eMadman/SmartSpin2k/Hardware/MODS/Direct Mount Mod/Bike Mount/reference photos/LeMond Revmaster/257341490_309686497794501_8044706802333533932_n.jpg

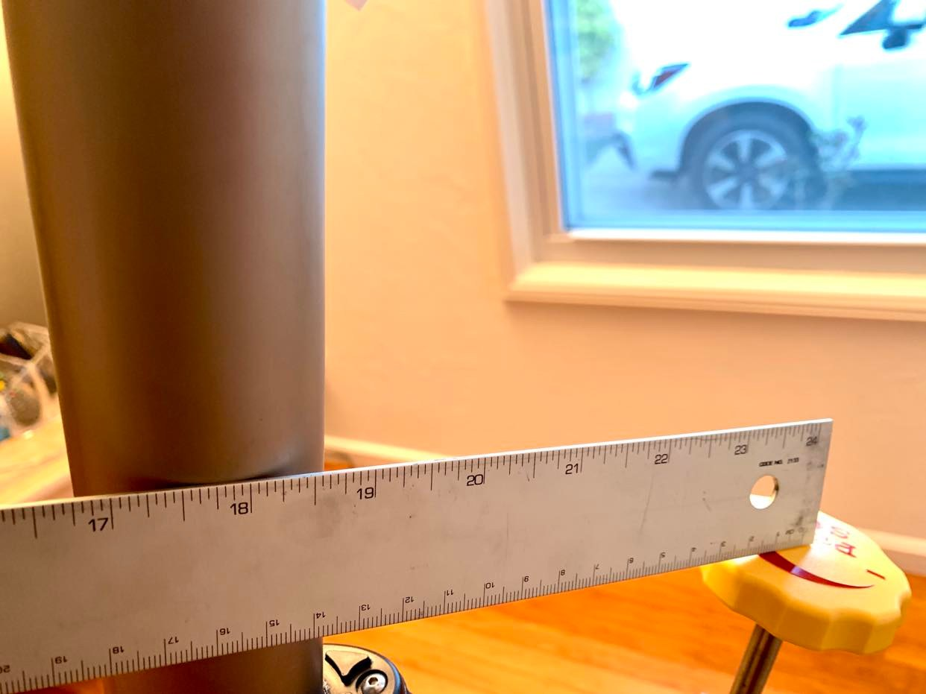
Hardware/MODS/Direct Mount Mod/Bike Mount/reference photos/LeMond Revmaster/257341490_309686497794501_8044706802333533932_n.jpg
