eMadman/SmartSpin2k/Hardware/MODS/Direct Mount Mod/Bike Mount/reference photos/LeMond Revmaster/257692339_471179641047132_6647679529000994123_n.jpg

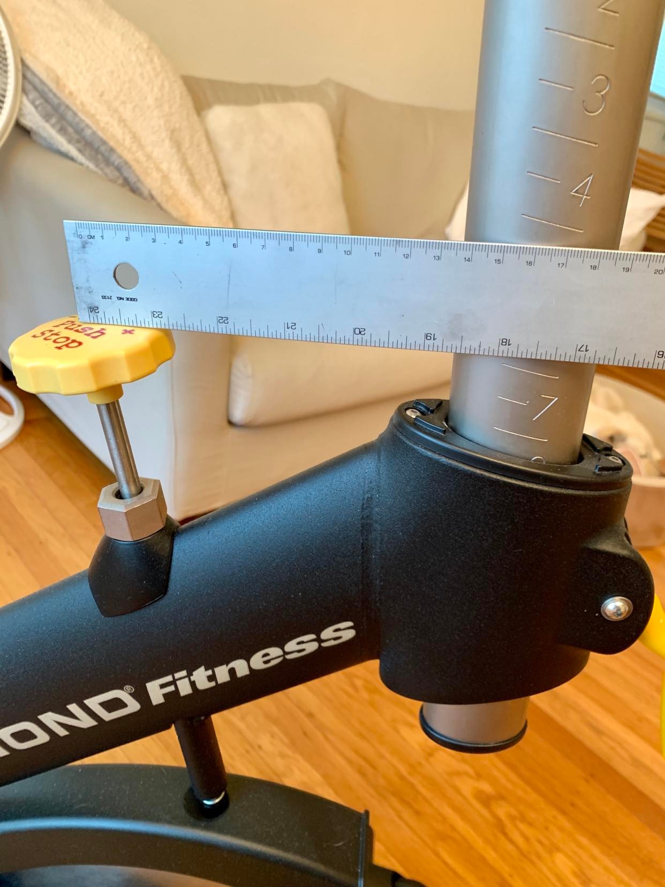
Hardware/MODS/Direct Mount Mod/Bike Mount/reference photos/LeMond Revmaster/257692339_471179641047132_6647679529000994123_n.jpg
