eMadman/SmartSpin2k/Hardware/MODS/Direct Mount Mod/Bike Mount/reference photos/LeMond Revmaster/258868316_243986774588775_1929228291426772959_n.jpg

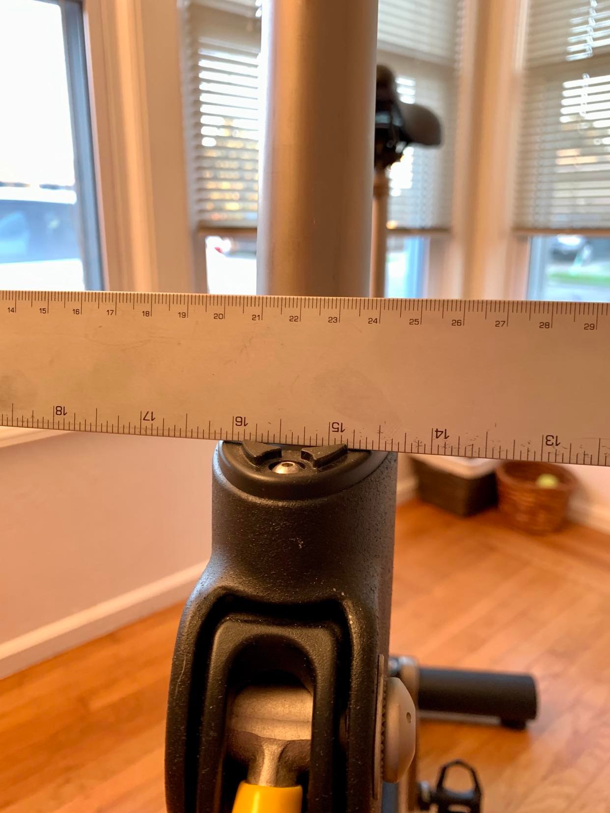
Hardware/MODS/Direct Mount Mod/Bike Mount/reference photos/LeMond Revmaster/258868316_243986774588775_1929228291426772959_n.jpg
