eMadman/SmartSpin2k/Hardware/MODS/Direct Mount Mod/Bike Mount/reference photos/LeMond Revmaster/261676048_6928923303847735_6218960208191569541_n (1).jpg

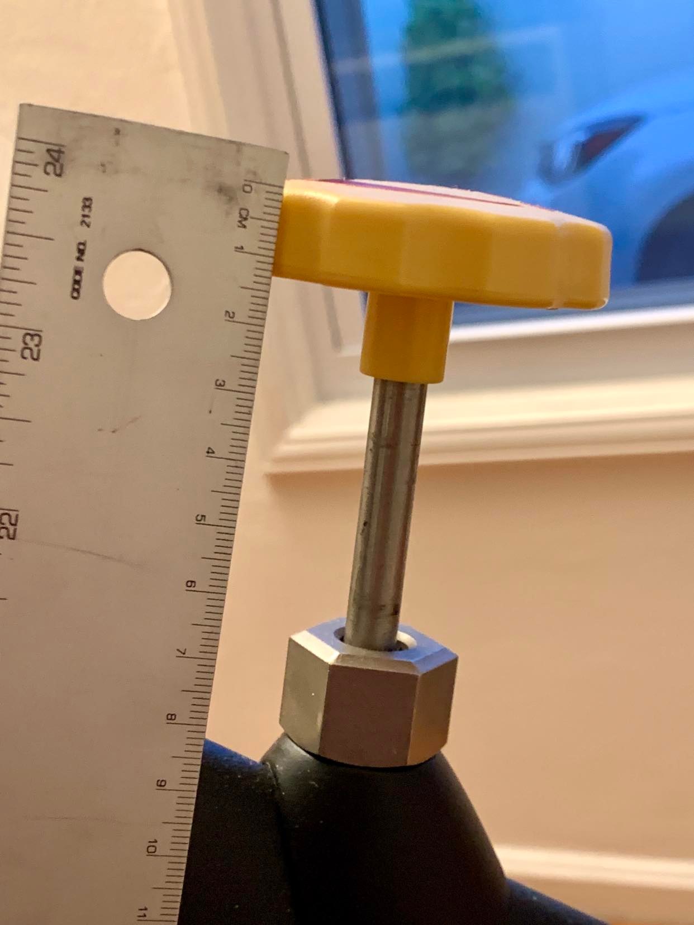
Hardware/MODS/Direct Mount Mod/Bike Mount/reference photos/LeMond Revmaster/261676048_6928923303847735_6218960208191569541_n (1).jpg
