eMadman/SmartSpin2k/Hardware/MODS/Direct Mount Mod/Bike Mount/reference photos/LeMond Revmaster/271715276_899334027414171_9209979407297314539_n.jpg

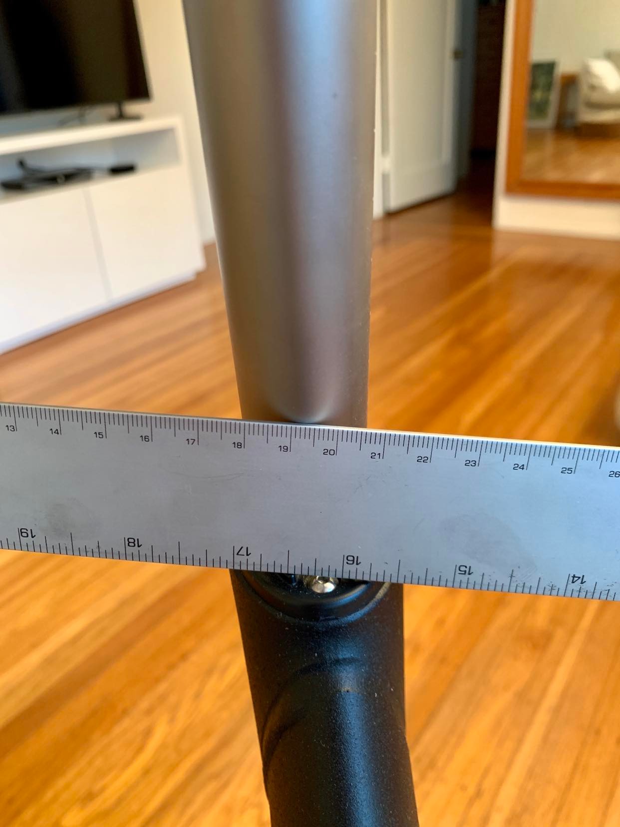
Hardware/MODS/Direct Mount Mod/Bike Mount/reference photos/LeMond Revmaster/271715276_899334027414171_9209979407297314539_n.jpg
