eMadman/SmartSpin2k/Hardware/MODS/Direct Mount Mod/Bike Mount/reference photos/LeMond Revmaster/272138903_289367993186954_1817032916722085885_n.jpg

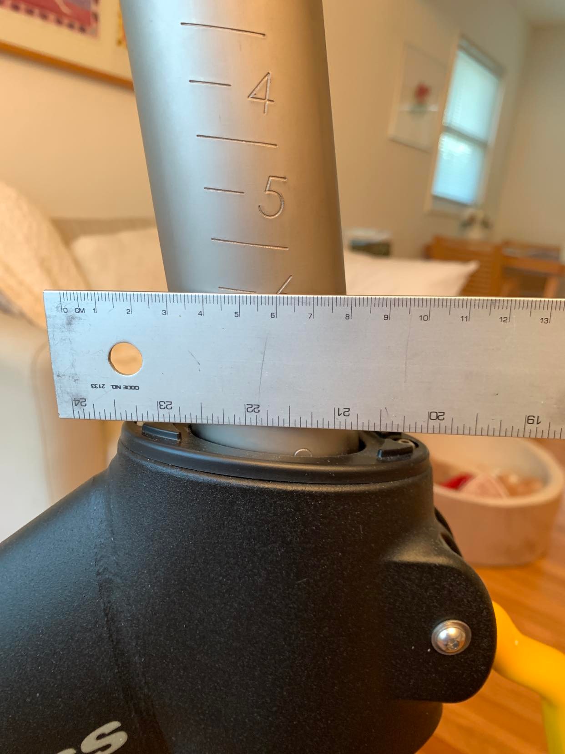
Hardware/MODS/Direct Mount Mod/Bike Mount/reference photos/LeMond Revmaster/272138903_289367993186954_1817032916722085885_n.jpg
