eMadman/SmartSpin2k/Hardware/MODS/Direct Mount Mod/Bike Mount/reference photos/Peloton/20220217_082705.jpg

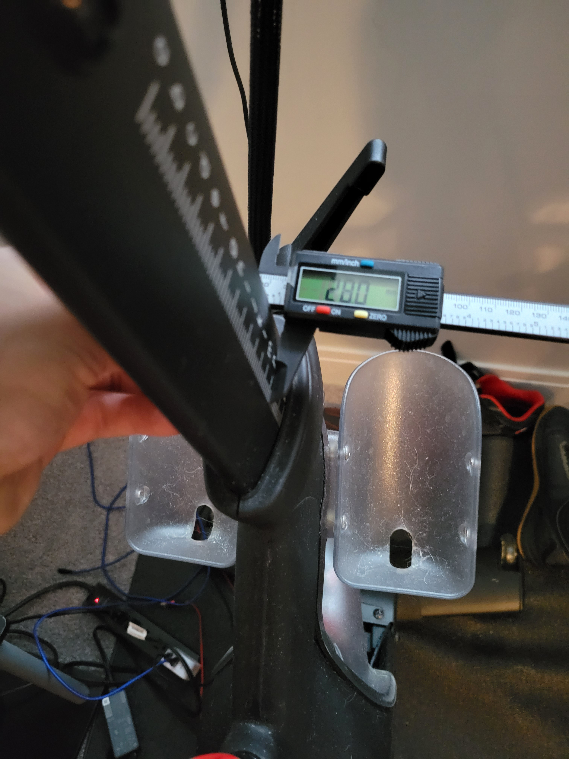
Hardware/MODS/Direct Mount Mod/Bike Mount/reference photos/Peloton/20220217_082705.jpg
