eMadman/SmartSpin2k/Hardware/MODS/Direct Mount Mod/Bike Mount/reference photos/Peloton/20220218_084504.jpg

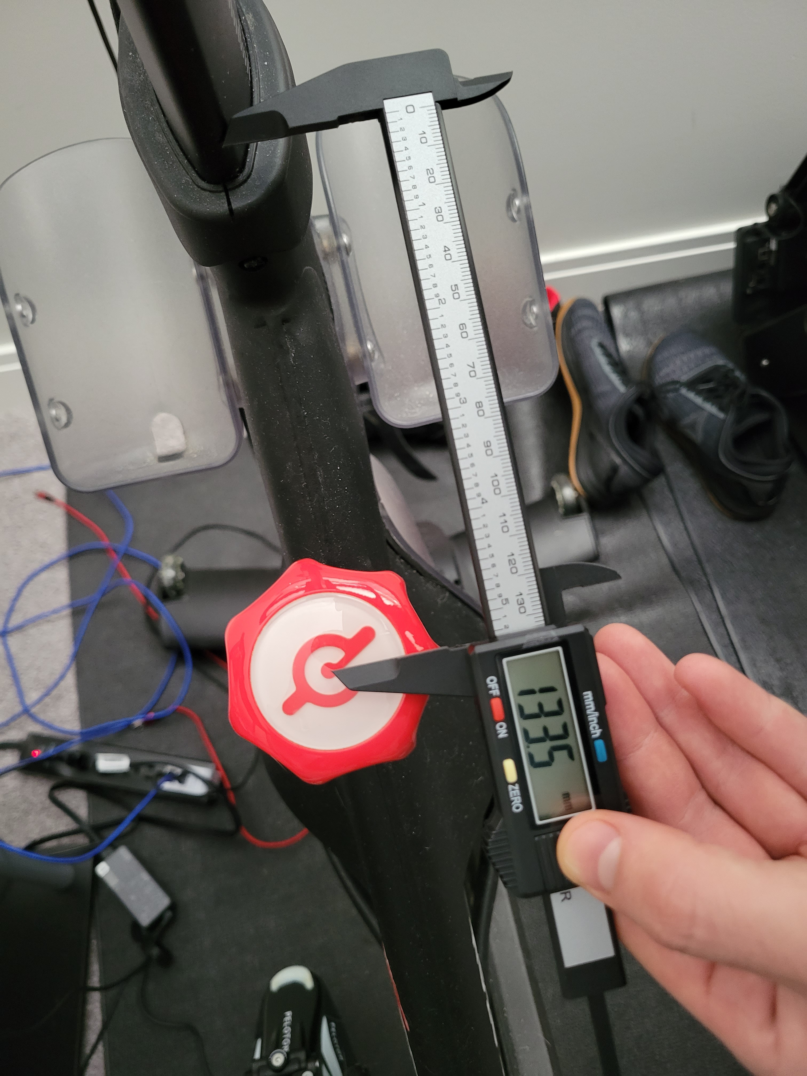
Hardware/MODS/Direct Mount Mod/Bike Mount/reference photos/Peloton/20220218_084504.jpg
