eMadman/SmartSpin2k/Hardware/MODS/Direct Mount Mod/Bike Mount/reference photos/Peloton/20220228_151501.jpg

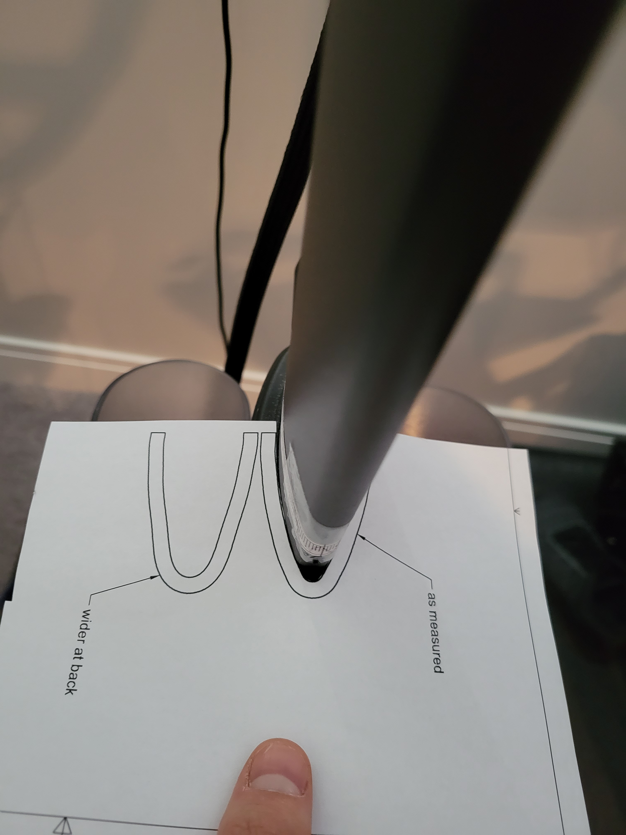
Hardware/MODS/Direct Mount Mod/Bike Mount/reference photos/Peloton/20220228_151501.jpg
