eMadman/SmartSpin2k/Hardware/MODS/Direct Mount Mod/Bike Mount/reference photos/Peloton/20220301_104258.jpg

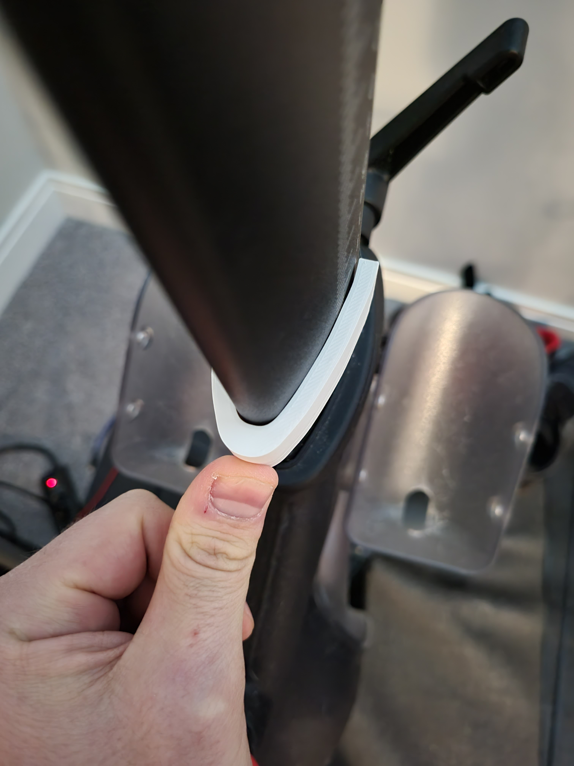
Hardware/MODS/Direct Mount Mod/Bike Mount/reference photos/Peloton/20220301_104258.jpg
