eMadman/SmartSpin2k/Hardware/MODS/Direct Mount Mod/Bike Mount/reference photos/Peloton/20220301_104306.jpg

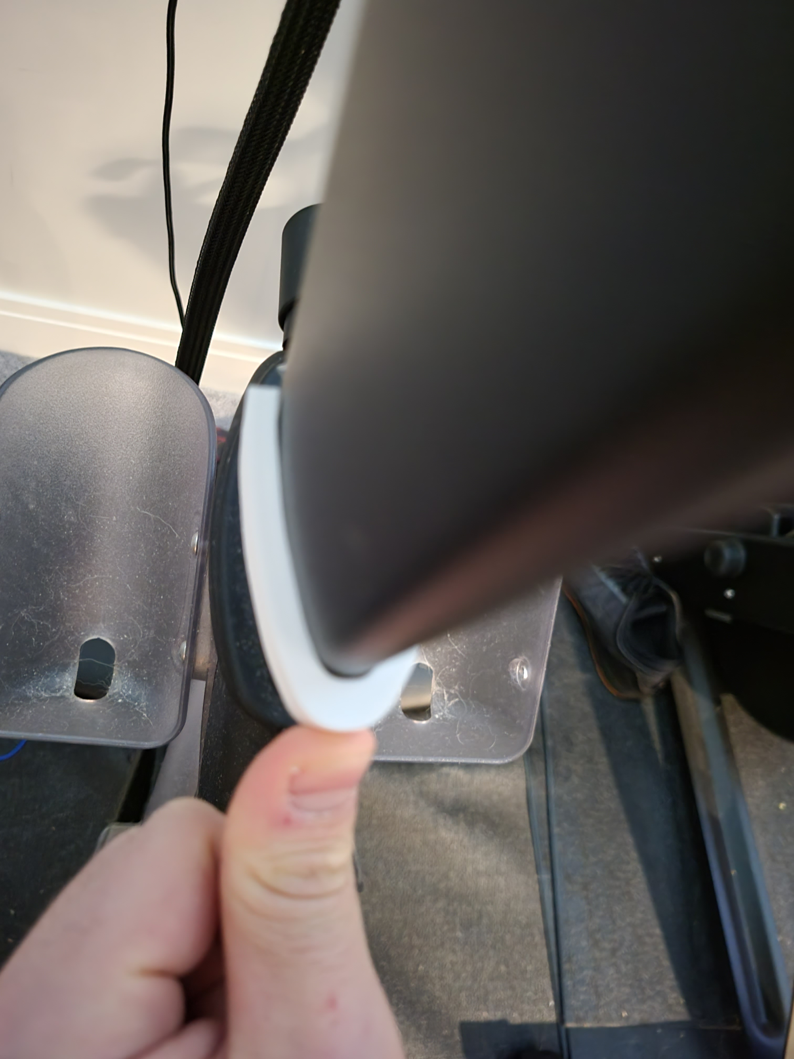
Hardware/MODS/Direct Mount Mod/Bike Mount/reference photos/Peloton/20220301_104306.jpg
