eMadman/SmartSpin2k/Hardware/MODs/Plastic Shifter/lid.stl

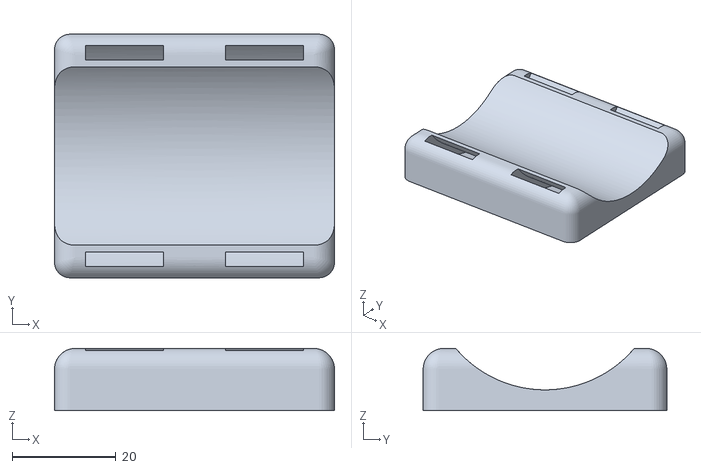
[picture p56: CAD file, 2023-01-07]
Hardware/MODs/Plastic Shifter/lid.stl
54.0 x 47.0 x 12.0
