eMadman/SmartSpin2k/Hardware/MODS/39.4mm motor/Case/Case/CAD/Body_Drawing_Right.STEP

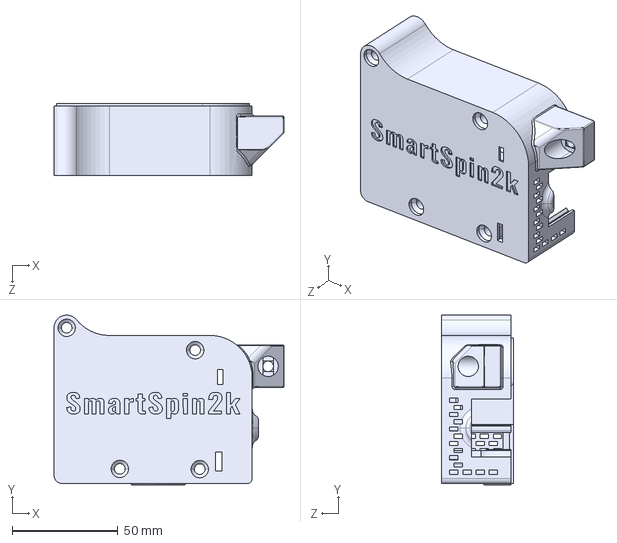
[picture p57: CAD file, 2023-07-26]
Hardware/MODS/39.4mm motor/Case/Case/CAD/Body_Drawing_Right.STEP
108.7 x 80.2 x 33.9 mm
