eMadman/SmartSpin2k/Hardware/MODS/Adjustable Arm/CAD/Schwinn IC4.step

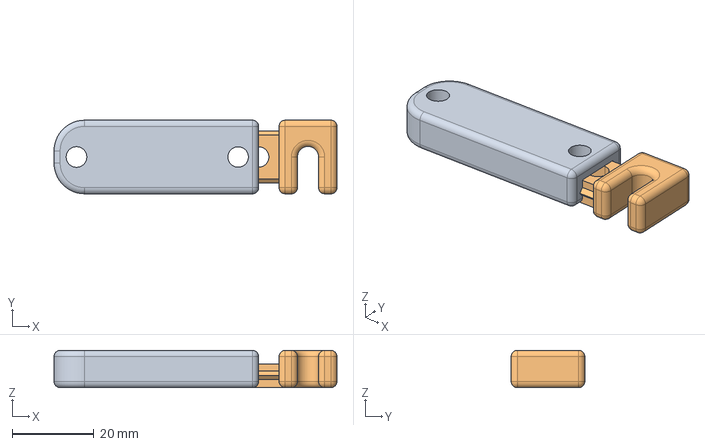
[picture p58: CAD file, 2023-04-02]
Hardware/MODS/Adjustable Arm/CAD/Schwinn IC4.step
69.2 x 18.0 x 9.10 mm
