eMadman/SmartSpin2k/Hardware/MODS/Case V2 - Ultra Short Mod/Case/CAD/Body_Drawing.STEP

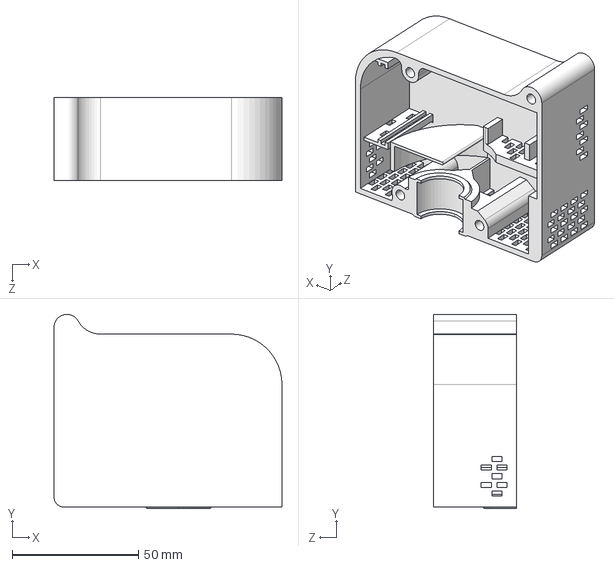
[picture p59: CAD file, 2022-03-06]
Hardware/MODS/Case V2 - Ultra Short Mod/Case/CAD/Body_Drawing.STEP
90.2 x 76.8 x 32.7 mm
