eMadman/SmartSpin2k/Hardware/MODS/39.4mm motor/Case/Case/CAD/Body_Drawing_Left.STEP

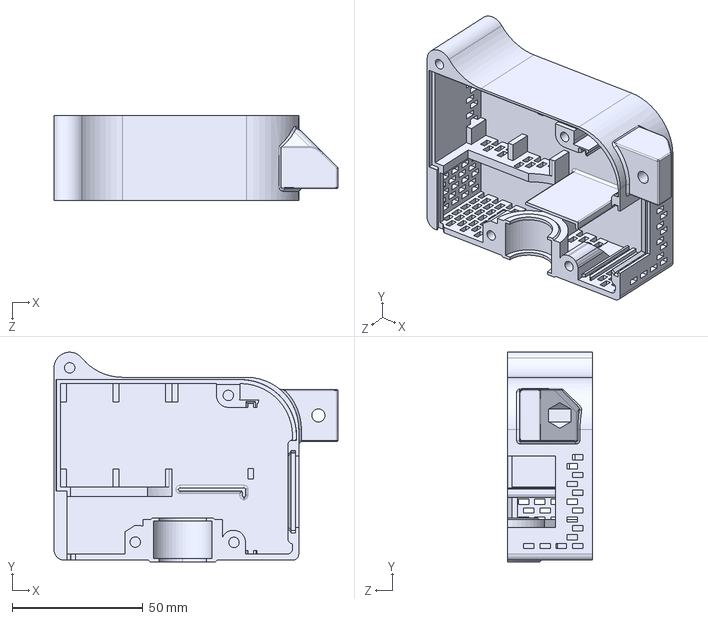
[picture p60: CAD file, 2023-07-26]
Hardware/MODS/39.4mm motor/Case/Case/CAD/Body_Drawing_Left.STEP
108.7 x 80.2 x 32.7 mm
