eMadman/SmartSpin2k/Hardware/MODS/Adjustable Arm/CAD/echelon connect sport.step

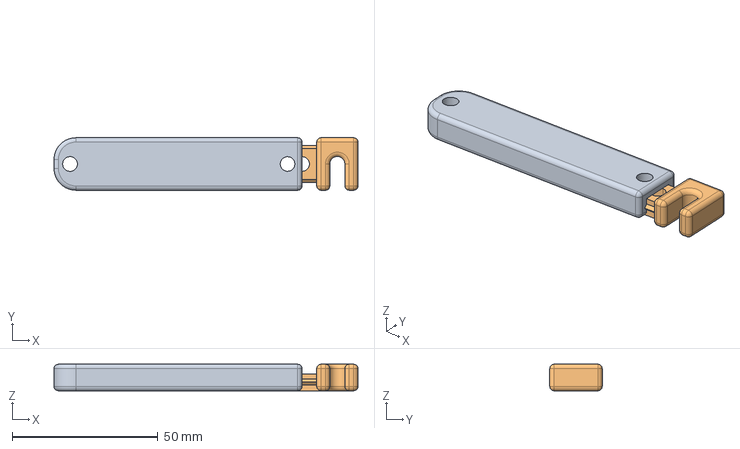
[picture p61: CAD file, 2023-04-02]
Hardware/MODS/Adjustable Arm/CAD/echelon connect sport.step
104.2 x 18.0 x 9.10 mm
