eMadman/SmartSpin2k/Hardware/MODS/Adjustable Arm/CAD/_ss2k arm - reference.step

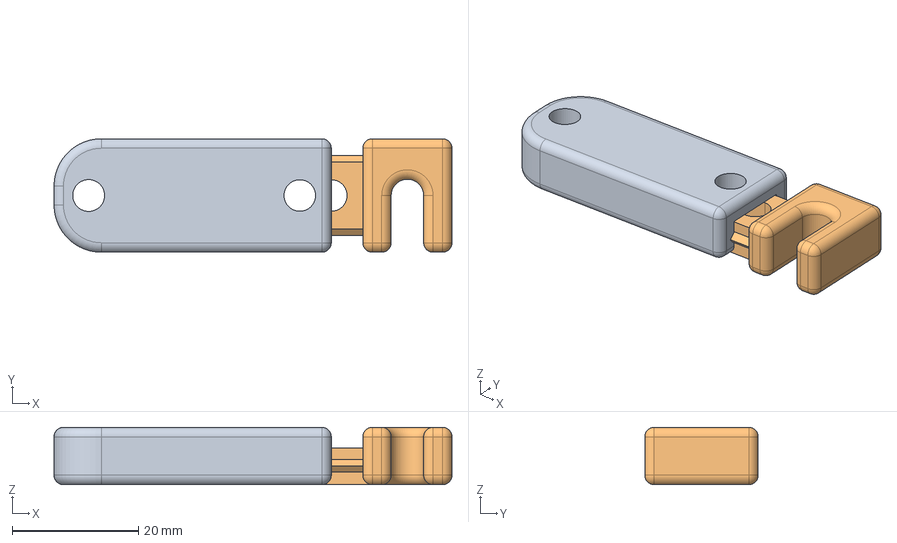
[picture p62: CAD file, 2023-04-02]
Hardware/MODS/Adjustable Arm/CAD/_ss2k arm - reference.step
63.1 x 18.0 x 9.10 mm
