eMadman/SmartSpin2k/Hardware/MODS/39.4mm motor/Case/Case/CAD/Window.STEP

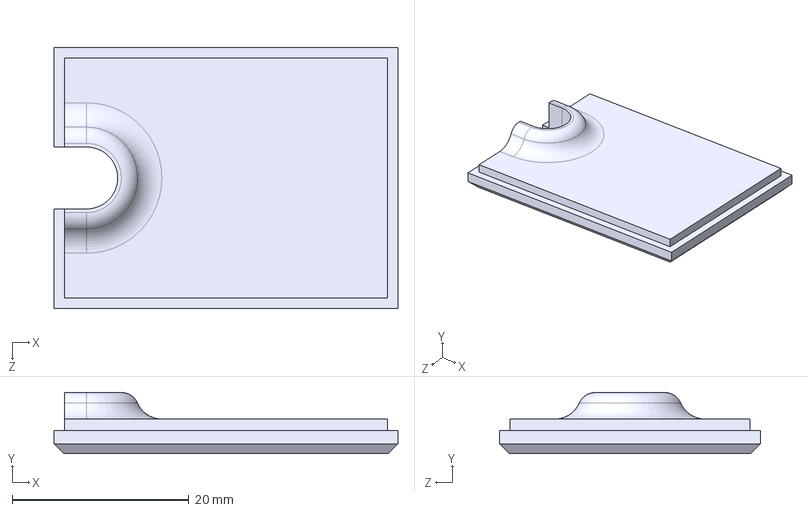
[picture p63: CAD file, 2023-07-26]
Hardware/MODS/39.4mm motor/Case/Case/CAD/Window.STEP
38.9 x 6.90 x 29.5 mm
