eMadman/SmartSpin2k/Hardware/MODS/39.4mm motor/Case/Case/CAD/Connectors/DC_PWR_CONN.STEP

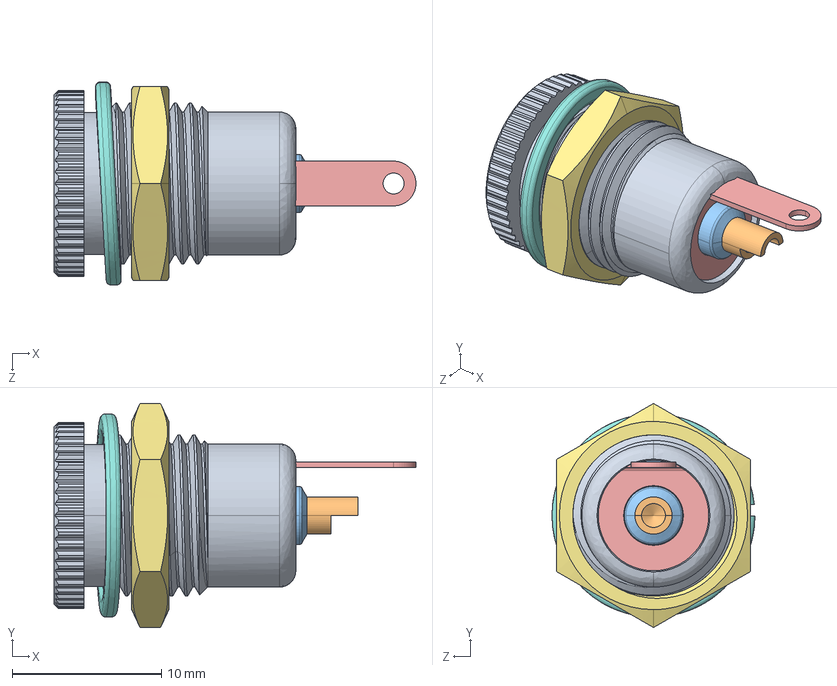
[picture p64: CAD file, 2023-07-26]
Hardware/MODS/39.4mm motor/Case/Case/CAD/Connectors/DC_PWR_CONN.STEP
24.2 x 15.0 x 13.6 mm
54-00063_Nickel Plating
