eMadman/SmartSpin2k/src/BLE_Setup.cpp

/*
 * Copyright (C) 2020  Anthony Doud & Joel Baranick
 * All rights reserved
 *
 * SPDX-License-Identifier: GPL-2.0-only
 */

#include "BLE_Common.h"
#include "Main.h"
#include "SS2KLog.h"
#include <ArduinoJson.h>
#include <NimBLEDevice.h>

void setupBLE() {  // Common BLE setup for both client and server
  SS2K_LOG(BLE_SETUP_LOG_TAG, "Starting Arduino BLE Client application...");
  BLEDevice::init(userConfig.getDeviceName());
  FTMSWrite = "";
  spinBLEClient.start();
  startBLEServer();

  xTaskCreatePinnedToCore(BLECommunications,      /* Task function. */
                          "BLECommunicationTask", /* name of task. */
                          5700,                   /* Stack size of task*/
                          NULL,                   /* parameter of the task */
                          1,                      /* priority of the task*/
                          &BLECommunicationTask,  /* Task handle to keep track of created task */
                          1);                     /* pin task to core */

  SS2K_LOG(BLE_SETUP_LOG_TAG, "BLE Notify Task Started");
  vTaskDelay(100 / portTICK_PERIOD_MS);
  if (strcmp(userConfig.getconnectedPowerMeter(), "none") != 0 || strcmp(userConfig.getconnectedHeartMonitor(), "none") != 0) {
    spinBLEClient.serverScan(true);
    SS2K_LOG(BLE_SETUP_LOG_TAG, "Scanning");
  }
  SS2K_LOG(BLE_SETUP_LOG_TAG, "%s %s", userConfig.getconnectedPowerMeter(), userConfig.getconnectedHeartMonitor());
  SS2K_LOG(BLE_SETUP_LOG_TAG, "End BLE Setup");
}
