eMadman/SmartSpin2k/include/HTTP_Server_Basic.h

/*
 * Copyright (C) 2020  Anthony Doud & Joel Baranick
 * All rights reserved
 *
 * SPDX-License-Identifier: GPL-2.0-only
 */

#pragma once

#include <Arduino.h>

#define HTTP_SERVER_LOG_TAG "HTTP_Server"

class HTTP_Server {
 private:
 public:
  void start();
  void stop();
  static void handleSpiffsFile();
  static void handleIndexFile();
  static void settingsProcessor();
  static void handleHrSlider();
  static void FirmwareUpdate();
  static void webClientUpdate(void *pvParameters);
};

#ifdef USE_TELEGRAM
#define SEND_TO_TELEGRAM(message) sendTelegram(message);

void sendTelegram(String textToSend);
void telegramUpdate(void *pvParameters);
#else
#define SEND_TO_TELEGRAM(message) (void)message
#endif

// wifi Function
class WiFi_Control {
 private:
 public:
  bool internetConnection;
  void start();
  void stop();
  static void maintain();
  WiFi_Control() { internetConnection = false; }
};

extern HTTP_Server httpServer;
extern WiFi_Control WiFiControl;
